WillACosta/dormin/pcb/revisions/rev-1.0__or/dormin_v1.kicad_sch

## KiCad design pcb/revisions/rev-1.0__or/dormin_v1.kicad_sch (2026-07-21)

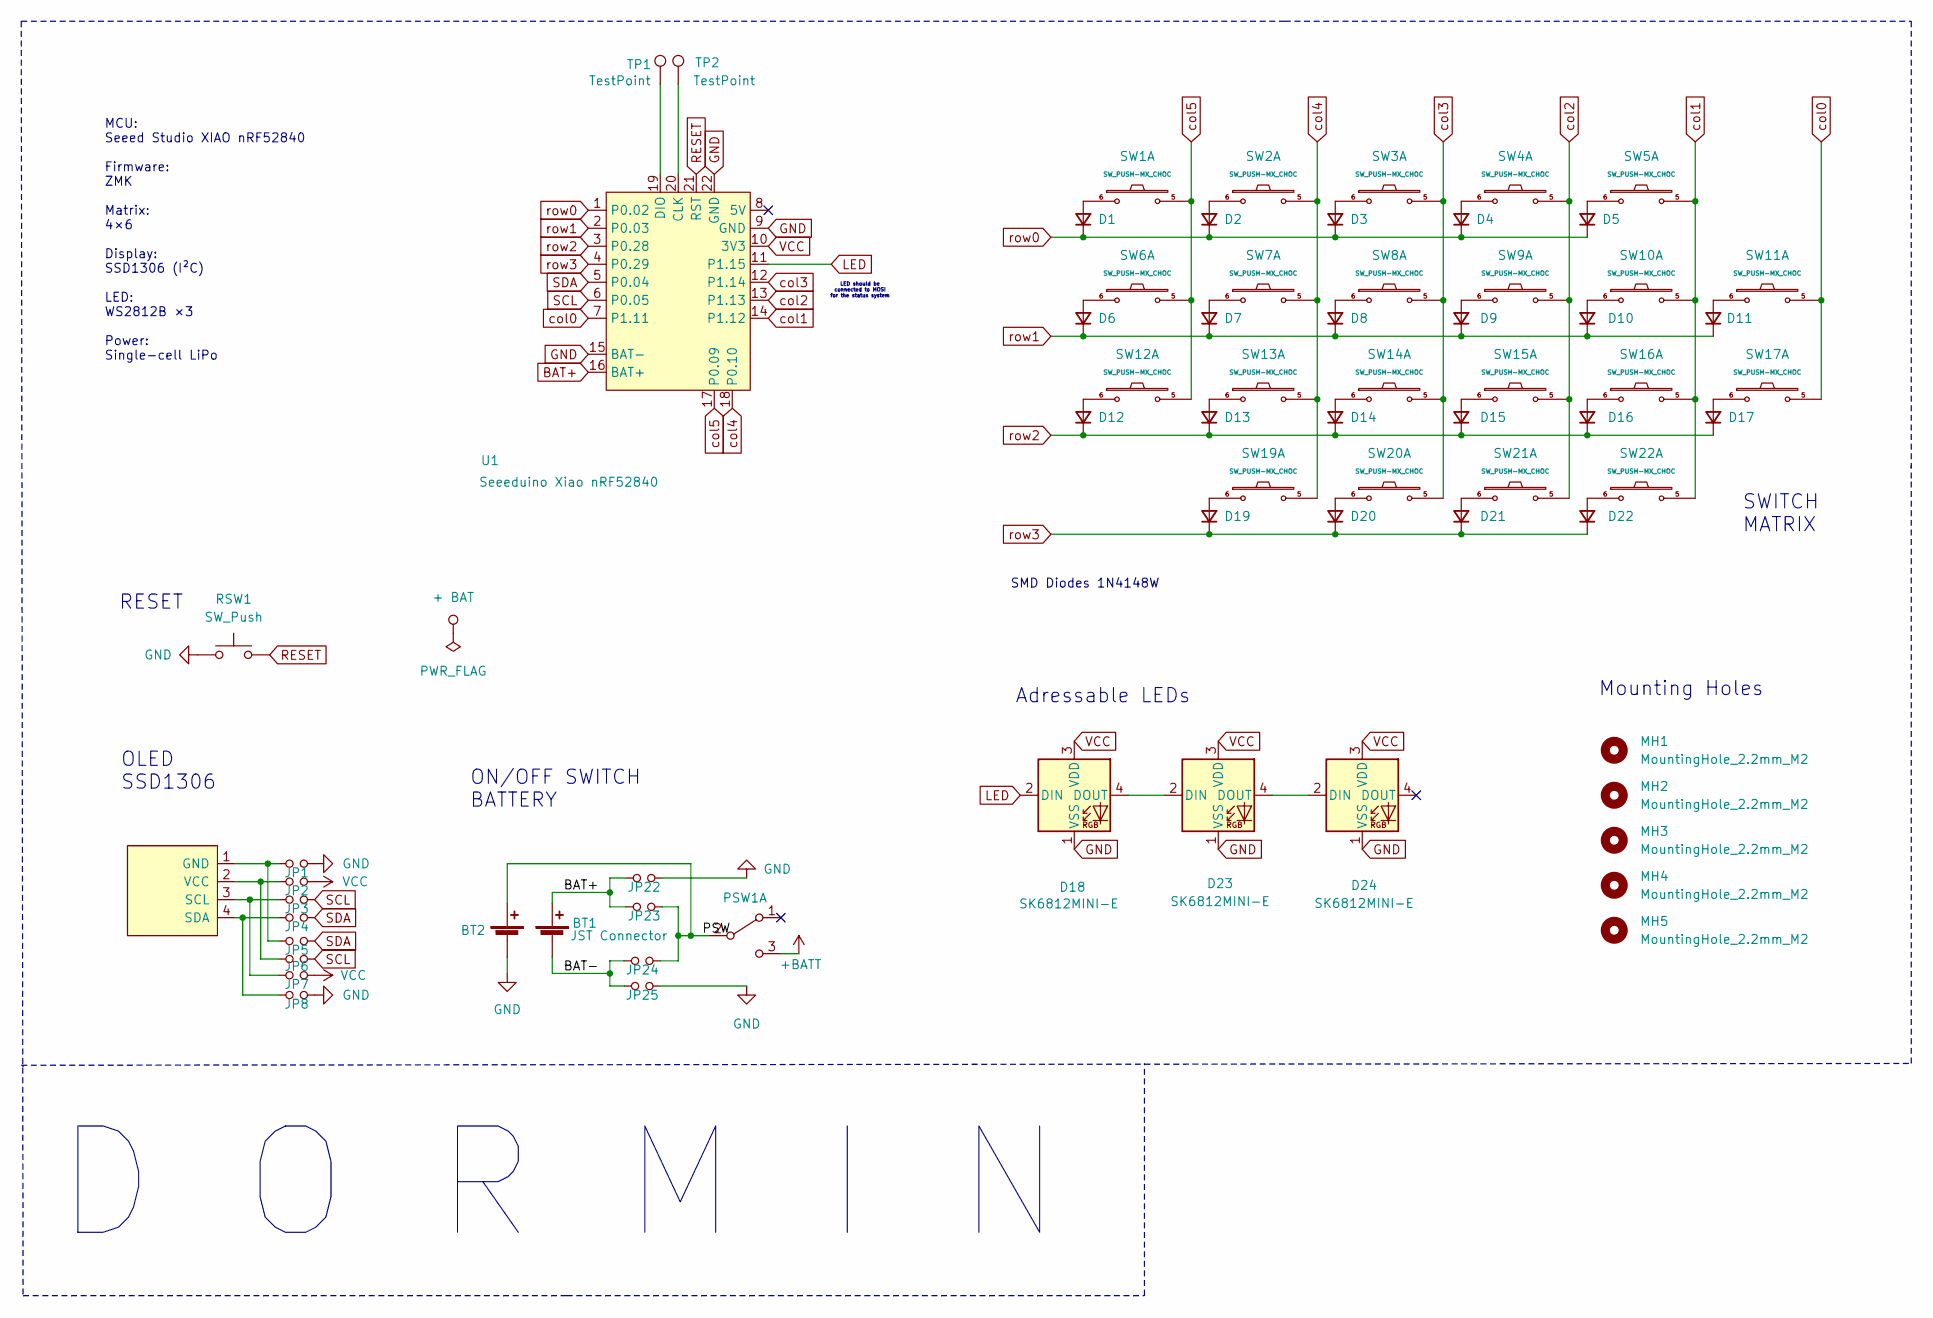
[picture p11: schematic dormin_v1.kicad_sch]

Parts:
BT1: JST Connector; JST_PH_reversible
BT2: Battery_Cell; custombatteryconnector_small
D1, D2, D3, D4, D5, D6, D7, D8, D9, D10, D11, D12, D13, D14, D15, D16, D17, D19, D20, D21, D22: D_Small; Diode_SOD123
D18, D23, D24: SK6812MINI-E; LED_SK6812MINI-E_3.2x2.8mm_P1.5mm_ReverseMount
JP1, JP2, JP3, JP4, JP5, JP6, JP7, JP8, JP22, JP23, JP24, JP25: Device_Jumper_NO_Small; Jumper
MH1, MH2, MH3, MH4, MH5: MountingHole_2.2mm_M2
OLED1: SSD1306; OLED_128x32
PSW1: SW_DPDT_x2; MSK12C02_reversible
RSW1: SW_Push; SW_Push_1P1T-MP_NO_Horizontal_Alps_SKRTLAE010_both_sides
SW1, SW2, SW3, SW4, SW5, SW6, SW7, SW8, SW9, SW10, SW11, SW12, SW13, SW14, SW15, SW16, SW17, SW19, SW20, SW21, SW22: SW_PUSH-MX_CHOC; SW_MXchoc_HS_1u
TP1, TP2: TestPoint
U1: Seeeduino Xiao nRF52840; Xiao_nRF52840_ACH

Connections:
+BATT: PSW1.3 (C)
BAT+: BT1.1 (+), JP22.1, JP23.1, U1.16 (BAT+)
BAT-: BT1.2 (-), JP24.1, JP25.1
GND: BT2.2 (-), D18.1 (VSS), D23.1 (VSS), D24.1 (VSS), JP1.2, JP8.2, JP22.2, JP25.2, RSW1.1, U1.9 (GND), U1.15 (BAT-), U1.22 (GND)
LED: D18.2 (DIN), U1.11 (P1.15)
unnamed: D1.2 (A), SW1.6
unnamed: D2.2 (A), SW2.6
unnamed: D3.2 (A), SW3.6
unnamed: D4.2 (A), SW4.6
unnamed: D5.2 (A), SW5.6
unnamed: D6.2 (A), SW6.6
unnamed: D7.2 (A), SW7.6
unnamed: D8.2 (A), SW8.6
unnamed: D9.2 (A), SW9.6
unnamed: D10.2 (A), SW10.6
unnamed: D11.2 (A), SW11.6
unnamed: D12.2 (A), SW12.6
unnamed: D13.2 (A), SW13.6
unnamed: D14.2 (A), SW14.6
unnamed: D15.2 (A), SW15.6
unnamed: D16.2 (A), SW16.6
unnamed: D17.2 (A), SW17.6
unnamed: D18.4 (DOUT), D23.2 (DIN)
unnamed: D19.2 (A), SW19.6
unnamed: D20.2 (A), SW20.6
unnamed: D21.2 (A), SW21.6
unnamed: D22.2 (A), SW22.6
unnamed: D23.4 (DOUT), D24.2 (DIN)
unnamed: JP1.1, JP5.1, OLED1.1 (GND)
unnamed: JP2.1, JP6.1, OLED1.2 (VCC)
unnamed: JP3.1, JP7.1, OLED1.3 (SCL)
unnamed: JP4.1, JP8.1, OLED1.4 (SDA)
unnamed: TP1.1, U1.19 (DIO)
unnamed: TP2.1, U1.20 (CLK)
PSW: BT2.1 (+), JP23.2, JP24.2, PSW1.2 (B)
RESET: RSW1.2, U1.21 (RST)
SCL: JP3.2, JP6.2, U1.6 (P0.05)
SDA: JP4.2, JP5.2, U1.5 (P0.04)
VCC: D18.3 (VDD), D23.3 (VDD), D24.3 (VDD), JP2.2, JP7.2, U1.10 (3V3)
col0: SW11.5, SW17.5, U1.7 (P1.11)
col1: SW5.5, SW10.5, SW16.5, SW22.5, U1.14 (P1.12)
col2: SW4.5, SW9.5, SW15.5, SW21.5, U1.13 (P1.13)
col3: SW3.5, SW8.5, SW14.5, SW20.5, U1.12 (P1.14)
col4: SW2.5, SW7.5, SW13.5, SW19.5, U1.18 (P0.10)
col5: SW1.5, SW6.5, SW12.5, U1.17 (P0.09)
row0: D1.1 (K), D2.1 (K), D3.1 (K), D4.1 (K), D5.1 (K), U1.1 (P0.02)
row1: D6.1 (K), D7.1 (K), D8.1 (K), D9.1 (K), D10.1 (K), D11.1 (K), U1.2 (P0.03)
row2: D12.1 (K), D13.1 (K), D14.1 (K), D15.1 (K), D16.1 (K), D17.1 (K), U1.3 (P0.28)
row3: D19.1 (K), D20.1 (K), D21.1 (K), D22.1 (K), U1.4 (P0.29)

Notes on the sheet:
SWITCH MATRIX
ON/OFF SWITCH BATTERY
Adressable LEDs
MCU: Seeed Studio XIAO nRF52840 Firmware: ZMK Matrix: 4×6 Display: SSD1306 (I²C) LED: WS2812B ×3 Power: Single-cell LiPo
Mounting Holes
OLED SSD1306
SMD Diodes 1N4148W
RESET
LED should be connected to MOSI for the status system
D O R M I N
